Moryu-Io/Roboken-FMSKF-robot-controller/src/ArmDrive/AD_joint_ics_servo.hpp

#ifndef AD_JOINT_ICS_SERVO_HPP_
#define AD_JOINT_ICS_SERVO_HPP_

#include "IcsHardSerialClass.h"

#include "AD_joint_base.hpp"
#include "global_config.hpp"

namespace ADT {

/**
 * @brief ICS通信方式サーボの関節を駆動するクラス
 * @note  TODO:HardwareSerial+DMAにすることで高速化したい
 *
 */
class JointIcsServo : public JointBase {
public:
  JointIcsServo(ConstParams &_c) : JointBase(_c){};

  void update() override;

  void init() override;

  /**
   * @brief 初期設定関数
   *
   * @param _p_ics_serial : begin済みのものを渡す
   * @param _id : このクラスで操作するサーボのID
   */
  void doinit(IcsHardSerialClass *_p_ics_serial, uint8_t _id) {
    p_ics_serial = _p_ics_serial;
    u8_id        = _id;
    init();
  }

protected:
  IcsHardSerialClass *p_ics_serial;

  uint8_t u8_id;
};

}; // namespace ADT

#endif
