Moryu-Io/Roboken-FMSKF-robot-controller/src/CameraGimbal/CG_task_main.hpp

#ifndef CG_TASK_MAIN_HPP_
#define CG_TASK_MAIN_HPP_

#include "global_config.hpp"

namespace CGT {

enum MSG_ID {
  REQ_INIT          = 0x01,
  REQ_MOVE_PITCH    = 0x10,
  REQ_DEFAULT_PITCH = 0x11,
  REQ_MOVE_YAW      = 0x12,
  REQ_DEFAULT_YAW   = 0x13,
  REQ_MOVE_PY       = 0x20,
  MSG_UNKNOWN       = 0xFF,
};

// Message共通変数
struct MsgCommon {
  uint8_t MsgId;
  uint8_t Sender;
  uint8_t Recv0;
  uint8_t Recv1;
};

// ID:0x10 REQ_MOVE_PITCH
// Positioning
struct MSG_ReqMovePitch {
  MsgCommon cmn;
  float     fl_pitch_deg;
};

// ID:0x12 REQ_MOVE_YAW
// Positioning
struct MSG_ReqMoveYaw {
  MsgCommon cmn;
  float     fl_yaw_deg;
};

// ID:0x20 REQ_MOVE_PY
// Positioning
struct MSG_ReqMovePY {
  MsgCommon cmn;
  float     fl_pitch_deg;
  float     fl_yaw_deg;
};


// Message共用体
union MSG_REQ {
  MsgCommon        common;
  MSG_ReqMovePitch move_pitch;
  MSG_ReqMoveYaw   move_yaw;
  MSG_ReqMovePY    move_py;
};

void prepare_task();
void main(void *params);

void send_req_msg(MSG_REQ *_msg);

float get_pitch_angle_deg();
float get_yaw_angle_deg();

}; // namespace CGT

#endif
