Moryu-Io/Roboken-FMSKF-robot-controller/src/ArmDrive/AD_task_main.hpp

#ifndef AD_TASK_MAIN_HPP_
#define AD_TASK_MAIN_HPP_

#include <interfaces/msg/time_angle.h>

namespace ADT {

enum MSG_ID {
  REQ_CHANGE_MODE    = 0x01,
  REQ_MOVE_POS       = 0x10,
  REQ_MOVE_TIMEANGLE = 0x11,
  REQ_DBG_TIMEANGLE  = 0xD1,
  MSG_UNKNOWN        = 0xFF,
};

// Message共通変数
struct MsgCommon {
  uint8_t MsgId;
  uint8_t Sender;
  uint8_t Recv0;
  uint8_t Recv1;
};

// ID:0x01 REQ_CHANGE_MODE
// MODE変更指示
struct MSG_ReqChangeMode {
  MsgCommon cmn;
  uint32_t  u32_mode_id;
  uint8_t   u8_forced; // 強制変更フラグ
  uint8_t   u8_resv;
};

enum MODE_ID {
  OFF,
  INIT,
  INIT_POS_MOVE, // 角度リセットはせずにトルクＯＮして初期位置移動
  POSITIONING,
  POSITIONING_SEQ,
  ERROR
};

// ID:0x10 REQ_MOVE_POS
// Positioning
struct MSG_ReqMovePos {
  MsgCommon cmn;
  uint32_t  u32_id;
  uint32_t  u32_dt_ms;
  float     fl_pos[5];
};

// ID:0x11 REQ_MOVE_TIMEANGLE
// Positioning
struct MSG_ReqMoveTimeAngle {
  MsgCommon                   cmn;
  uint32_t                    u32_id;
  uint32_t                    u32_len;
  interfaces__msg__TimeAngle *ptr_tAng;
};

// ID:0xD1 REQ_DBG_TIMEANGLE
// Positioning
struct MSG_ReqDebugTimeAngle {
  MsgCommon cmn;
  uint32_t  u32_id;
};

// Message共用体
union MSG_REQ {
  MsgCommon             common;
  MSG_ReqChangeMode     change_mode;
  MSG_ReqMovePos        move_pos;
  MSG_ReqMoveTimeAngle  time_angle;
  MSG_ReqDebugTimeAngle dbg_time_angle;
};

void prepare_task();
void main(void *params);

void send_req_msg(MSG_REQ *_msg);

uint32_t get_status_movepos_proc(uint32_t _cmdid);
uint32_t get_status_timeangle_proc(uint32_t _cmdid);

void get_arm_angle_rad(float *_fl_ang);


}; // namespace ADT

#endif
