Moryu-Io/Roboken-FMSKF-robot-controller/src/ArmDrive/AD_mode_positioning_seq_debug_data.hpp

#ifndef AD_MODE_POSITIONING_SEQ_DEBUG_DATA_HPP_
#define AD_MODE_POSITIONING_SEQ_DEBUG_DATA_HPP_

#include "AD_mode_positioning_seq.hpp"
#include "global_config.hpp"

namespace ADT {

ADTModePositioningSeq::PosCmdSeq *get_poscmdseq_debug();

};

#endif
